DigitalLivestock/biotope-lite/hardware/schematic/biotope_lite_rev1.0.kicad_sch

## KiCad design hardware/schematic/biotope_lite_rev1.0.kicad_sch (2026-04-12)

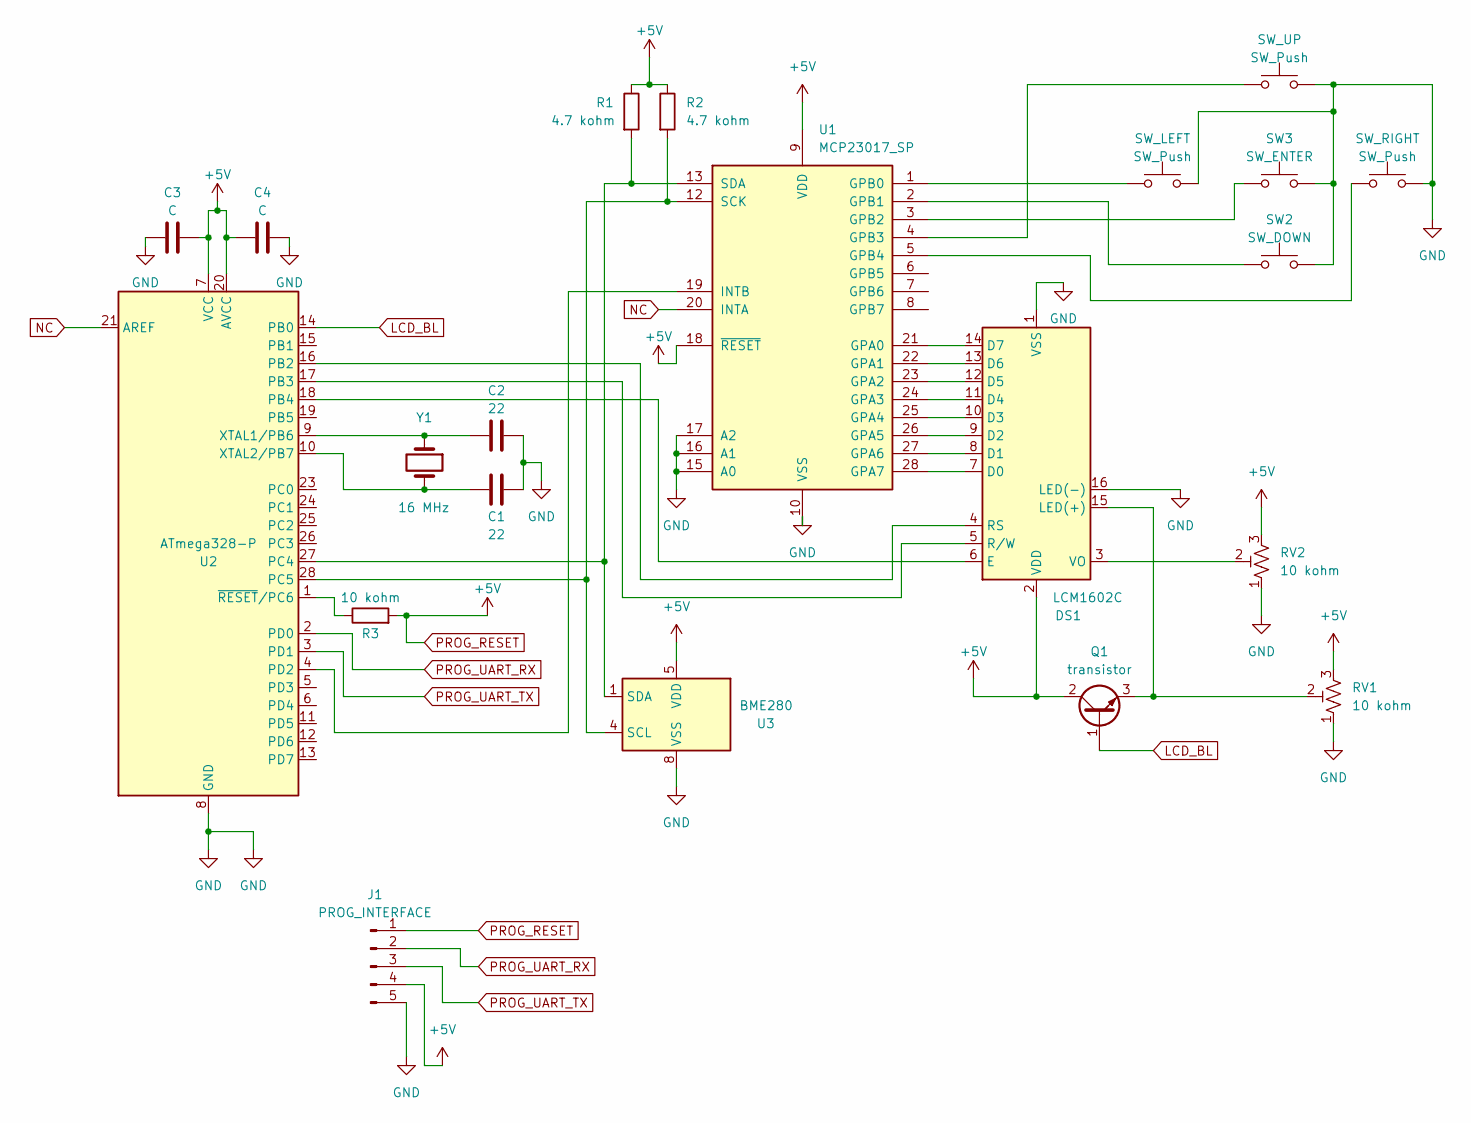
[picture p2: schematic biotope_lite_rev1.0.kicad_sch]

Parts:
C1, C2: 22
C3, C4: C
DS1: LCM1602C; WC1602A
J1: PROG_INTERFACE
Q1: transistor; TO-220-3_Vertical
R1, R2: 4.7 kohm
R3: 10 kohm
RV1, RV2: 10 kohm
SW2: SW_DOWN
SW3: SW_ENTER
SW_LEFT: SW_Push
SW_RIGHT: SW_Push
SW_UP: SW_Push
U1: MCP23017_SP; DIP-28_W7.62mm
U2: ATmega328-P; DIP-28_W7.62mm
U3: BME280
Y1: 16 MHz

Connections:
+5V: C3.1, C4.2, DS1.2 (VDD), J1.1, J1.4, Q1.2 (C), R1.1, R2.1, R3.2, RV1.3, RV2.3, U1.9 (VDD), U1.18 (~RESET), U2.7 (VCC), U2.20 (AVCC), U3.5 (VDD)
GND: C1.1, C2.1, C3.2, C4.1, DS1.1 (VSS), DS1.16 (LED(-)), J1.5, RV1.1, RV2.1, SW2.2, SW3.2, SW_LEFT.2, SW_RIGHT.2, SW_UP.2, U1.10 (VSS), U1.15 (A0), U1.16 (A1), U1.17 (A2), U2.8 (GND), U2.22 (GND), U3.8 (VSS), U3.9 (VSS)
LCD_BL: Q1.1 (B), U2.14 (PB0)
NC: U1.20 (INTA), U2.21 (AREF)
unnamed: C1.2, U2.10 (XTAL2/PB7), Y1.2
unnamed: C2.2, U2.9 (XTAL1/PB6), Y1.1
unnamed: DS1.3 (VO), RV2.2
unnamed: DS1.4 (RS), U2.16 (PB2)
unnamed: DS1.5 (R/W), U2.17 (PB3)
unnamed: DS1.6 (E), U2.18 (PB4)
unnamed: DS1.7 (D0), U1.28 (GPA7)
unnamed: DS1.8 (D1), U1.27 (GPA6)
unnamed: DS1.9 (D2), U1.26 (GPA5)
unnamed: DS1.10 (D3), U1.25 (GPA4)
unnamed: DS1.11 (D4), U1.24 (GPA3)
unnamed: DS1.12 (D5), U1.23 (GPA2)
unnamed: DS1.13 (D6), U1.22 (GPA1)
unnamed: DS1.14 (D7), U1.21 (GPA0)
unnamed: DS1.15 (LED(+)), Q1.3 (E), RV1.2
unnamed: R1.2, U1.13 (SDA), U2.27 (PC4), U3.1 (SDA)
unnamed: R2.2, U1.12 (SCK), U2.28 (PC5), U3.4 (SCL)
unnamed: R3.1, U2.1 (~RESET/PC6)
unnamed: SW2.1, U1.2 (GPB1)
unnamed: SW3.1, U1.3 (GPB2)
unnamed: SW_LEFT.1, U1.1 (GPB0)
unnamed: SW_RIGHT.1, U1.5 (GPB4)
unnamed: SW_UP.1, U1.4 (GPB3)
unnamed: U1.19 (INTB), U2.4 (PD2)
PROG_UART_RX: J1.2, U2.2 (PD0)
PROG_UART_TX: J1.3, U2.3 (PD1)
